skiselev/xi_8088/KiCad/8088-SBC.sch

## KiCad design KiCad/8088-SBC.sch (2023-10-24)

Schematic: 8088-SBC.sch

Parts:
BT1: CR2032
BUS1: BUSAT_HOST
C1, C2, C3, C4, C5, C6, C7, C8, C9, C10, C11, C12, C13, C14, C15, C16, C17, C18, C19, C20, C21, C22, C23, C24, C25, C26, C27, C28, C29, C30, C31, C32, C33, C34, C35, C36, C37, C38, C39, C40, C41, C42, C43, C44, C45, C46: 0.1uF
C47, C48, C49, C50, C51: 10uF
C52, C53: 33pF
C54: 5-30pF
C55, C56, C57, C58: 47pF
C59: 0.01uF
D1: 1N4148
D2: POWER_LED
D3: TURBO_LED
F1: 1.1A
HOLE1, HOLE2: CONN_1
J1: RESET
J2: TURBO
J3: IRQ12
J4: ISA16_ENA
J5: CLR_NVRAM
P1: KEYBOARD
P2: MOUSE
P3: SPEAKER
P4: +PLED
P5: +TLED
Q1: PN2222A
R1: 100k
R2, R4, R5: 470
R3: 10k
R6: 1k
R7: 33
R8, R9: 510
RR1, RR2, RR3, RR4, RR5: 10k
RR6: 470
SP1: SPEAKER
SW1: RESET
SW2: MEM_CFG
SW3: NUM_WS
U1: 8284
U2: 8088
U3: 8087
U4: 8288
U5, U6: 8259
U7: 8237
U8: 8254
U9: 8242KBD
U10: DS12885
U11, U12: AS6C4008
U13: 29F010
U14: 74LS670
U15, U16, U17: 74F573
U18, U19, U20, U21: 74F245
U22, U23: 74F244
U24, U25, U26: 74ALS175
U27, U28: 74ALS139
U29: 74ALS138
U30: 74LS92
U31, U32, U33: 74ALS74
U34, U35: 74ALS32
U36: 74ALS20
U37: 74ALS11
U38: 74LS06
U39, U40: 74ALS04
U41, U42: 74ALS02
U43, U44, U45: 74ALS00
U46: 24MHz
X1: 14.31818MHz
X2: 32768Hz

Notes on the sheet:
- For NMOS 8284 (U1) replace C52 and C53 with 510 ohm resistors R8 and R9 - SW2.7 must be ON if SW2.5 or SW2.6 are ON - One and only one of SW3 switches must be ON - VGA BIOS usually mapped to 0C0000h-0C7FFFh make sure that SW2.1 is OFF when using VGA
Notes
SW2.1 - ON = Map 0C0000h-0C7FFFh to RAM SW2.2 - ON = Map 0C8000h-0CFFFFh to RAM SW2.3 - ON = Map 0D0000h-0D7FFFh to RAM SW2.4 - ON = Map 0D8000h-0DFFFFh to RAM SW2.5 - ON = Map 0E0000h-0E7FFFh to RAM SW2.6 - ON = Map 0E8000h-0EFFFFh to RAM SW2.7 - ON = 64 KiB ROM, starting from 0F0000h OFF = 128 Ki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
Settings
Bypass Capacitors
Pull-up Resistors
LEDs
ISA Bus
Memory Chip Select Logic
Keyboard Controller
Input / Output Chip Select Logic
Real Time Clock (RTC)
Interrupt Controllers (PICs)
Port B (61h), NMI Logic, and Speaker
Timer (PIT)
Clock and Reset Logic
Bus Arbitration and Wait Logic
Memory
DMA Controller and Page Register
X-Bus Transceivers
Processor Module
